KytorIndustries/bnctoscart/photos/DSC_7845.jpg

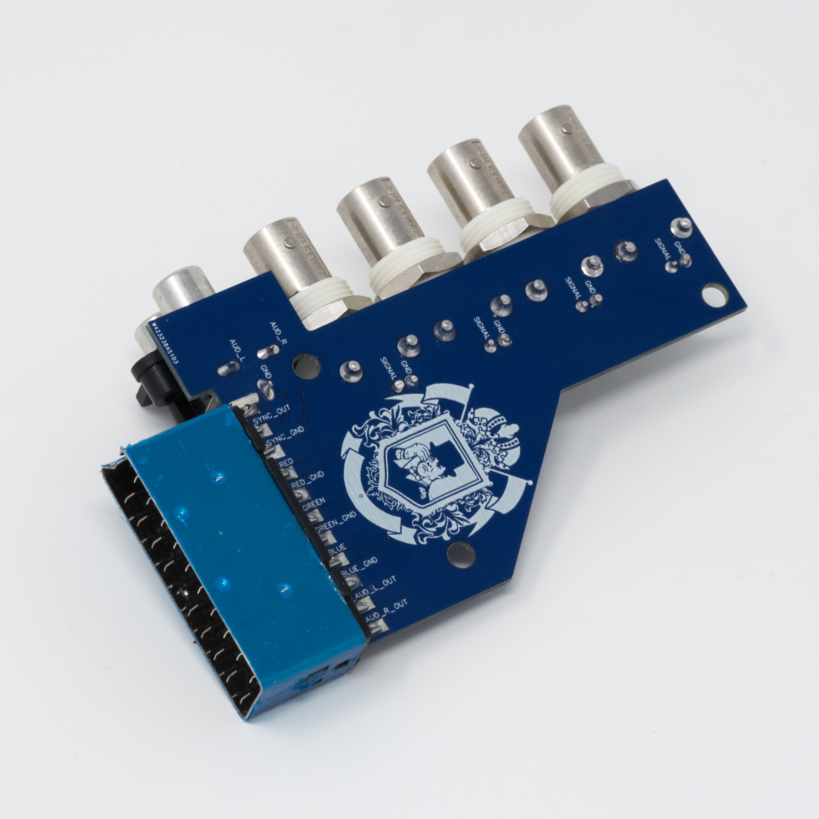
photos/DSC_7845.jpg
